picotouch/DC-DIY-UPS/images/2_1_back.png

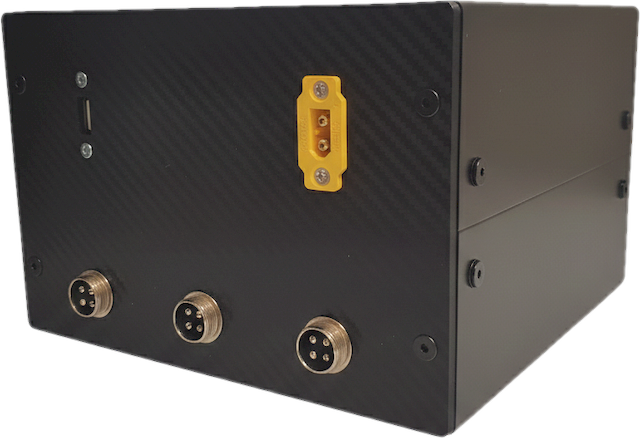
images/2_1_back.png
