picotouch/DC-DIY-UPS/images/2_1_front_and_side.png

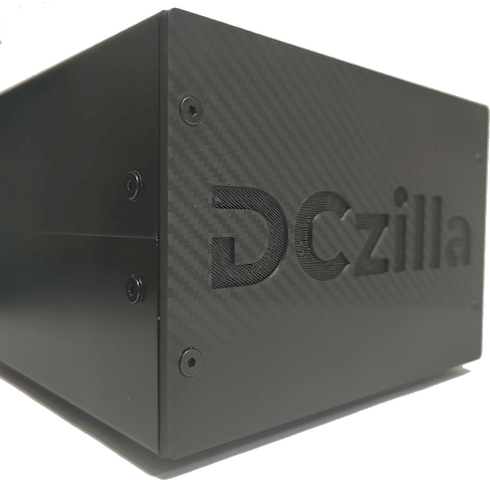
images/2_1_front_and_side.png
