picotouch/DC-DIY-UPS/images/LTC3780_WD2002SJ_LowVoltageCutout.jpg

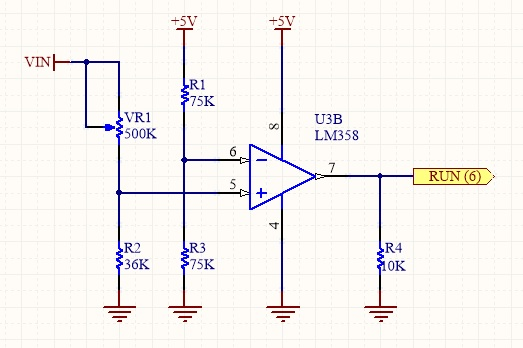
images/LTC3780_WD2002SJ_LowVoltageCutout.jpg
